poko56/StrikeSense/ml_pipeline/confusion_matrix.png

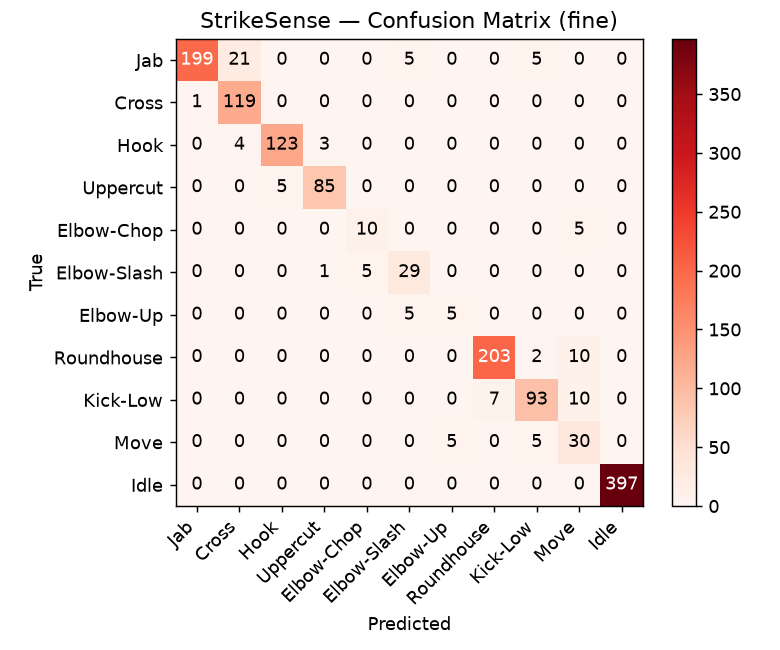
ml_pipeline/confusion_matrix.png
